UniversalScientificTechnologies/MRAKOMER04/CAM_AMA/V2.pdf

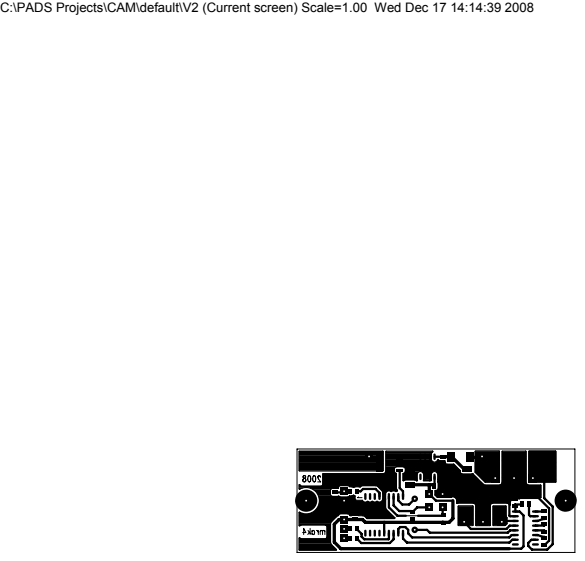
[picture p17: page 1]

C:\PADS Projects\CAM\default\V2 (Current screen) Scale=1.00 Wed Dec 17 14:14:39 2008
