UniversalScientificTechnologies/MRAKOMER04/CAM_AMA/V2_USB.pdf

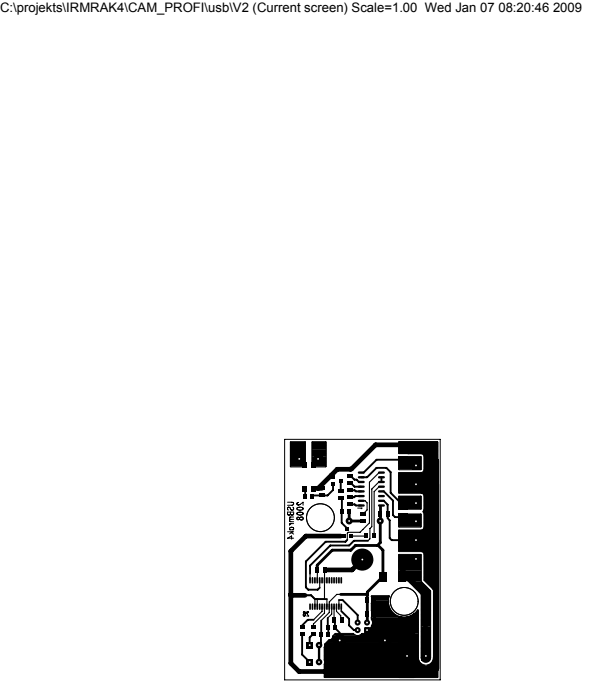
[picture p18: page 1]

C:\projekts\IRMRAK4\CAM_PROFI\usb\V2 (Current screen) Scale=1.00 Wed Jan 07 08:20:46 2009
