UniversalScientificTechnologies/MRAKOMER04/SW/setcidla/main.h

#include <16F877A.h>
#device adc=8

#FUSES NOWDT                    //No Watch Dog Timer
#FUSES HS                       //High speed Osc (> 4mhz)
#FUSES NOPUT                    //No Power Up Timer
#FUSES NOPROTECT                //Code not protected from reading
#FUSES NODEBUG                  //No Debug mode for ICD
#FUSES NOBROWNOUT               //No brownout reset
#FUSES NOLVP                    //No low voltage prgming, B3(PIC16) or B5(PIC18) used for I/O
#FUSES NOCPD                    //No EE protection
#FUSES NOWRT                    //Program memory not write protected

#use delay(clock=20000000) // 14318180)
//#use rs232(baud=9600,parity=N,xmit=PIN_C6,rcv=PIN_C7,bits=8) // Pro USART
#use rs232(baud=9600,parity=N,bits=8,xmit=PIN_B7,rcv=PIN_B6) // Pro PICkit2

#use i2c(Master,Fast,sda=PIN_C4,scl=PIN_C3,SMBUS)
